viesturz/Voron2Toolbox/STL/Box/[tpu] StrainRelief.stl

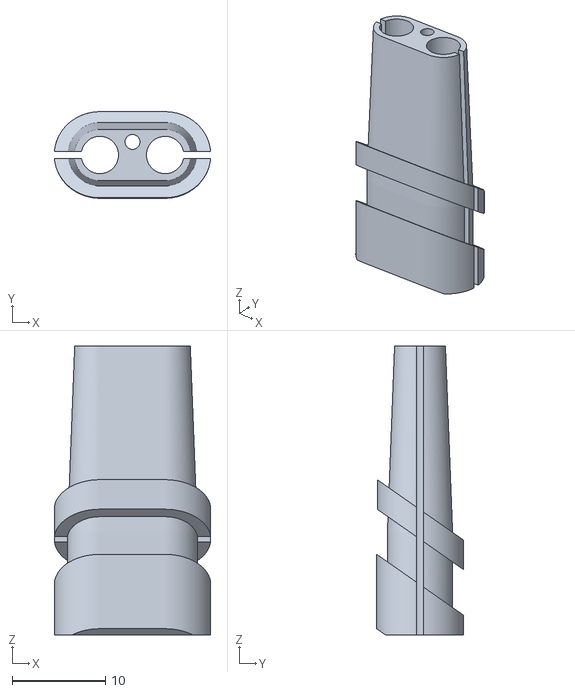
[picture p21: CAD file, 2023-07-04]
STL/Box/[tpu] StrainRelief.stl
16.8 x 9.29 x 31.0
