viesturz/Voron2Toolbox/STL/Toolhead/Stealthburner/StrainReliefAdapter.stl

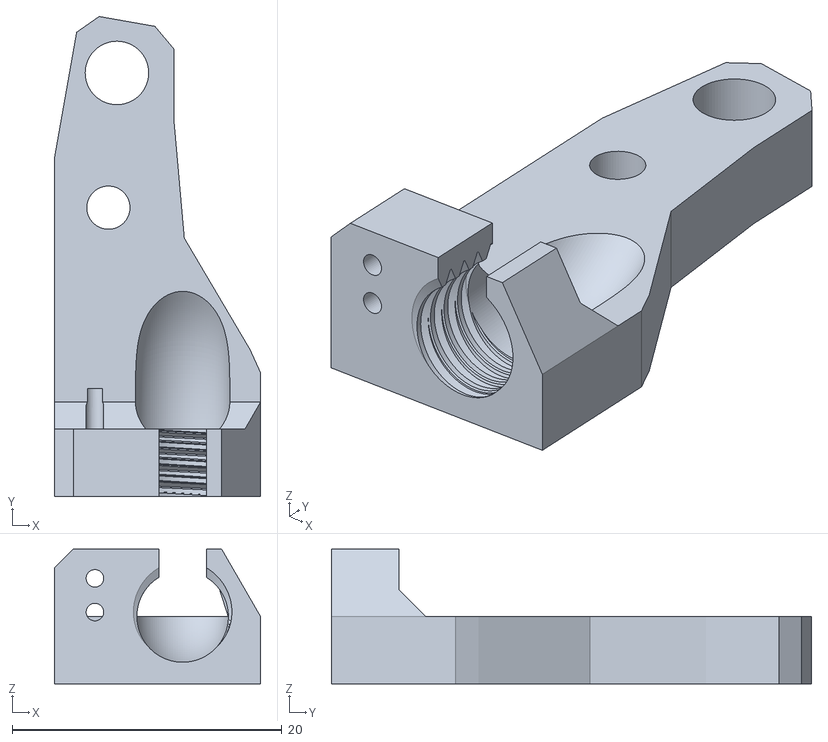
[picture p22: CAD file, 2023-07-07]
STL/Toolhead/Stealthburner/StrainReliefAdapter.stl
15.3 x 35.6 x 10.0
